biancascirtocea/OpenBook-TSC/Images/Display.png

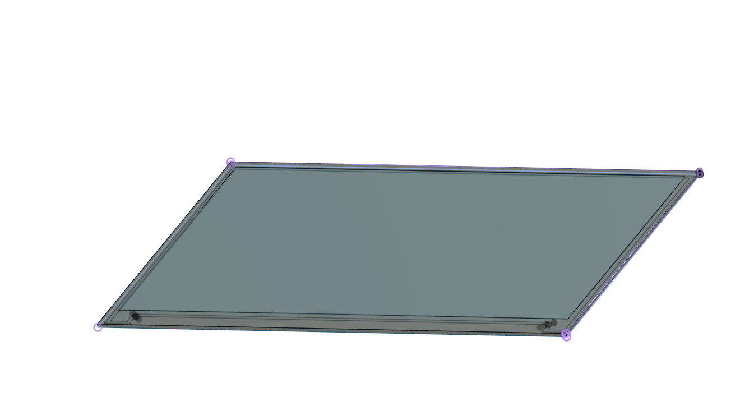
Images/Display.png
